321tutur123/axion-pad/hardware/cad/body/v_perso axion.3mf

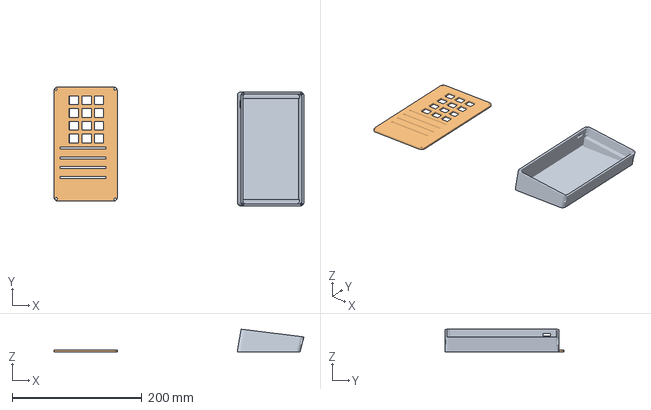
[picture p21: CAD file, 2026-04-22]
hardware/cad/body/v_perso axion.3mf
385.3 x 183.5 x 35.0 mm
Corps1
Corps3
